arntsonl/OpenFightStick/boombox/Side Panel Screw.stl

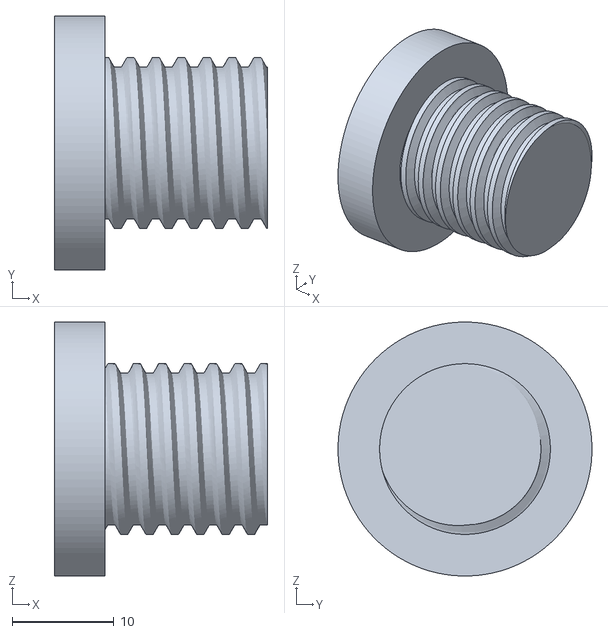
[picture p20: CAD file, 2023-01-07]
boombox/Side Panel Screw.stl
21.0 x 25.0 x 25.0
